EloyRamirez/MiniTar/images/1-MiniTar Schem.png

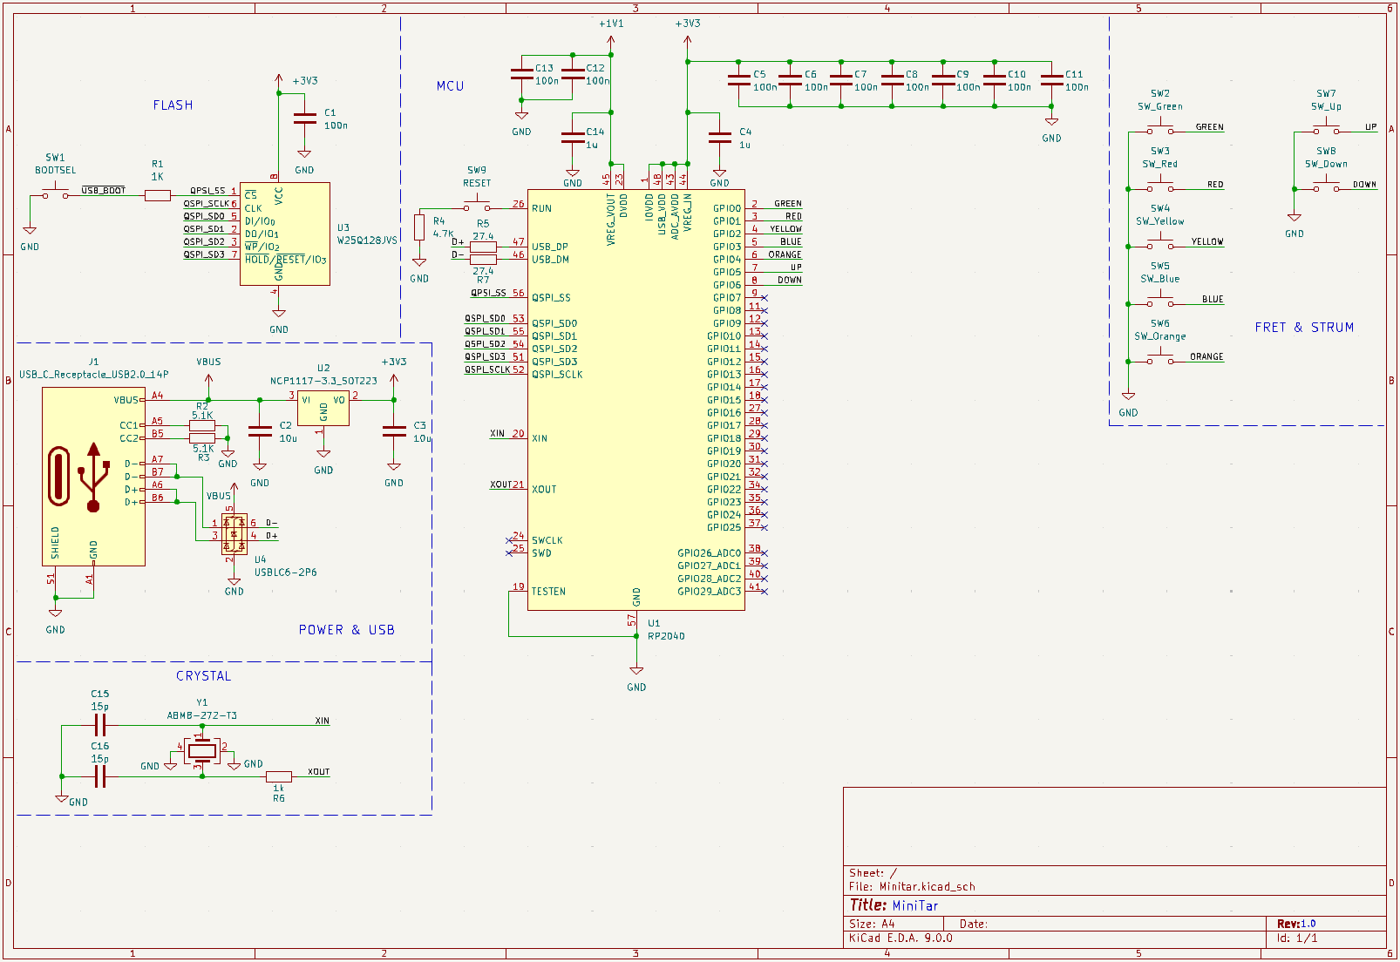
images/1-MiniTar Schem.png
