EloyRamirez/MiniTar/images/3-Copper Front Closeup.png

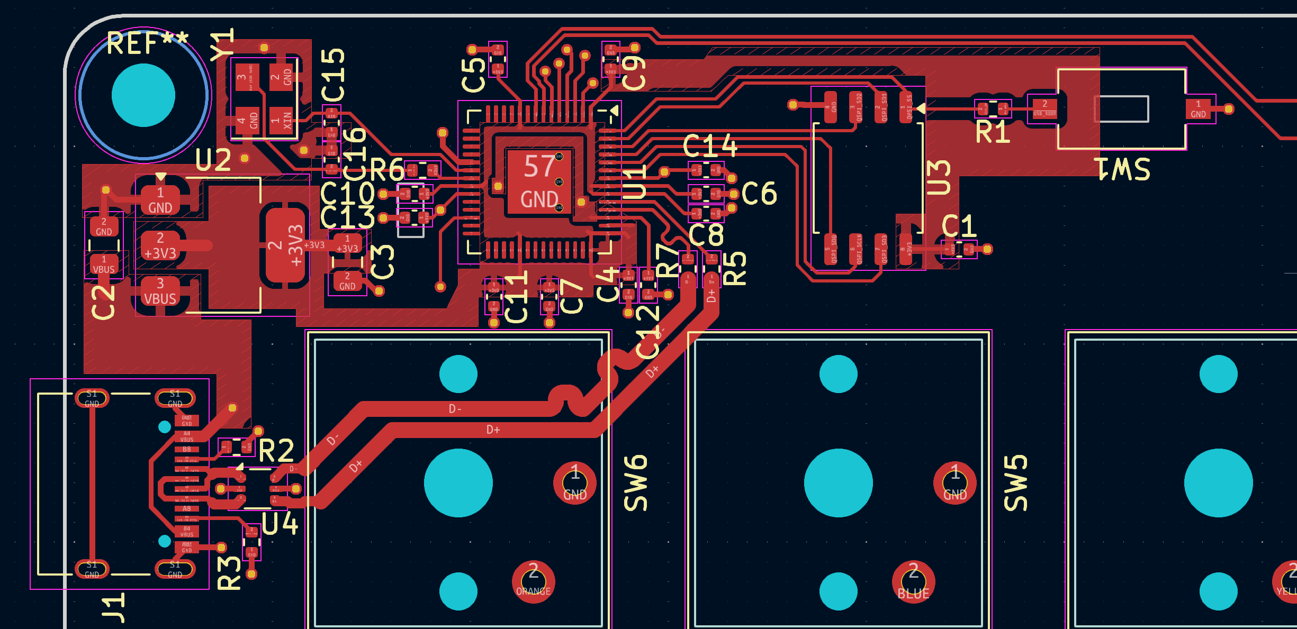
images/3-Copper Front Closeup.png
