EloyRamirez/MiniTar/images/7-Both Copper Layers.png

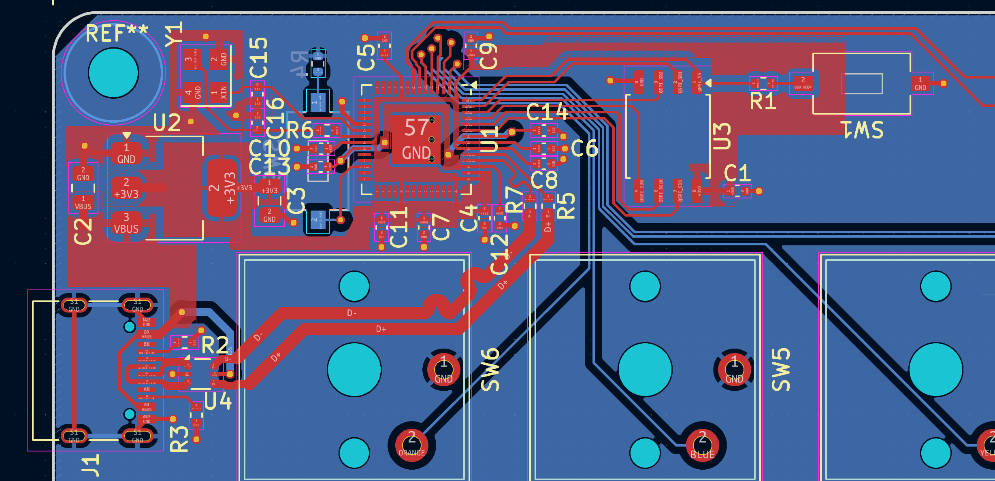
images/7-Both Copper Layers.png
