EloyRamirez/MiniTar/images/Case.png

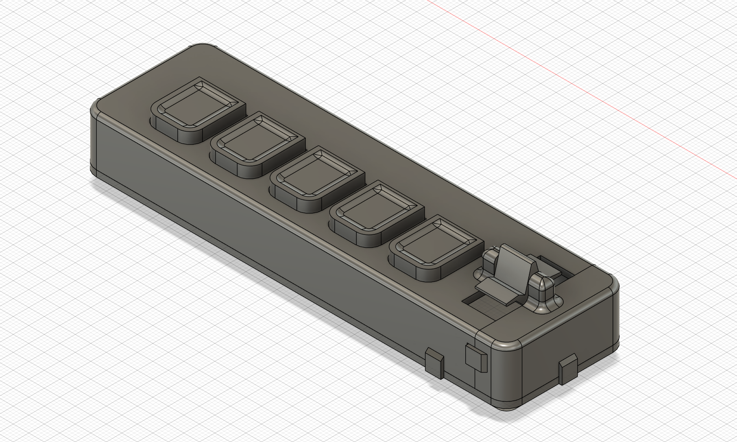
images/Case.png
